k5utd/Cobalt-Cowboy/Hardware/KiCAD/Computing_System.kicad_sch

## KiCad design Hardware/KiCAD/Computing_System.kicad_sch (2023-11-19, an earlier design)

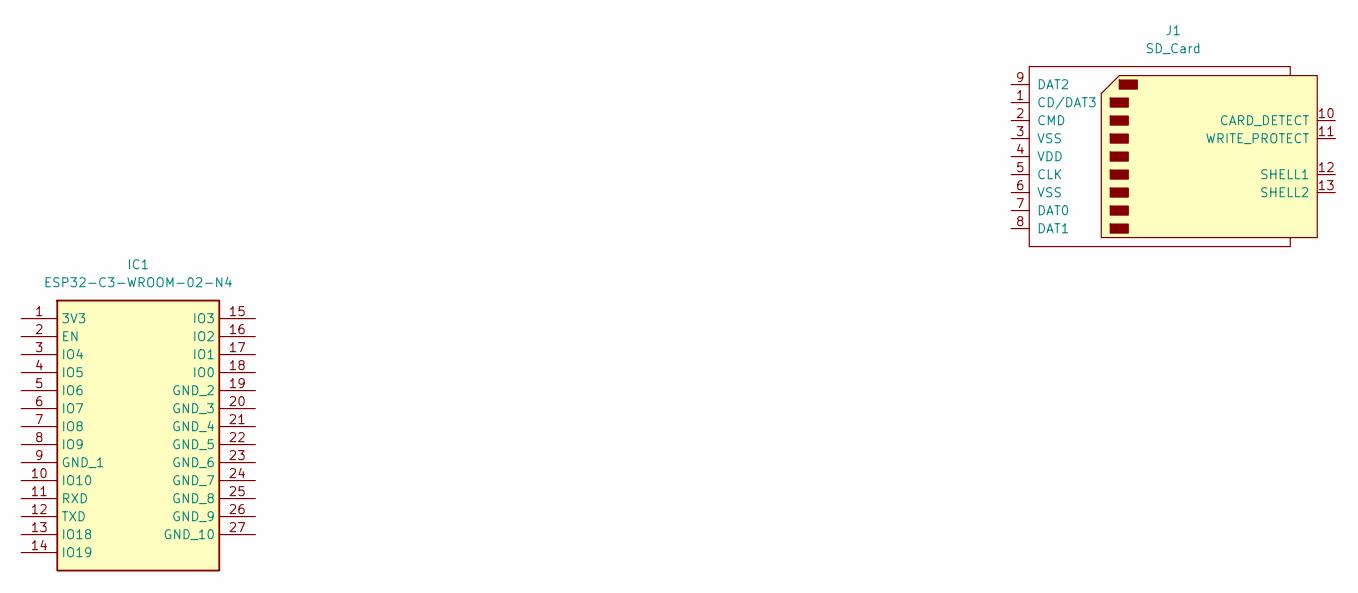
[picture p7: schematic Computing_System.kicad_sch]

Parts:
IC1: ESP32-C3-WROOM-02-N4; ESP32C3WROOM02N4; Manufacturer_Part_Number ESP32-C3-WROOM-02-N4; Mouser Part Number 356-ESP32C3WROOM02N4
J1: SD_Card
